tobycm/skibidi-usb-charger-hub/pcb/render_back.png

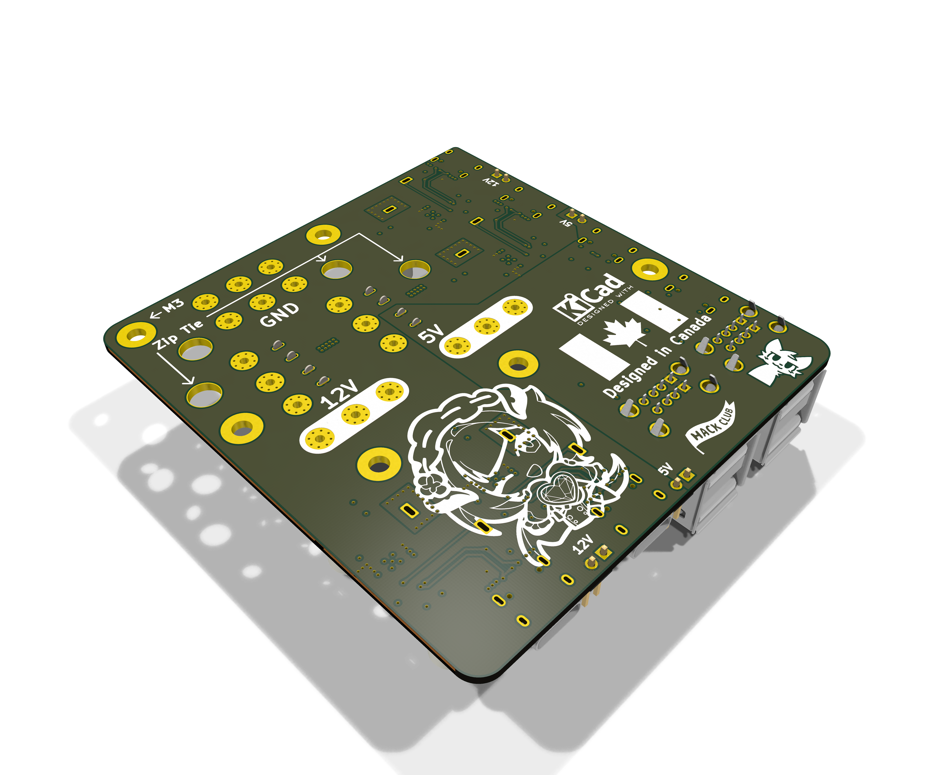
pcb/render_back.png
